niranjannt/Local-Music-Streaming-Pipeline/web_app/frontend/src/assets/need2.jpg

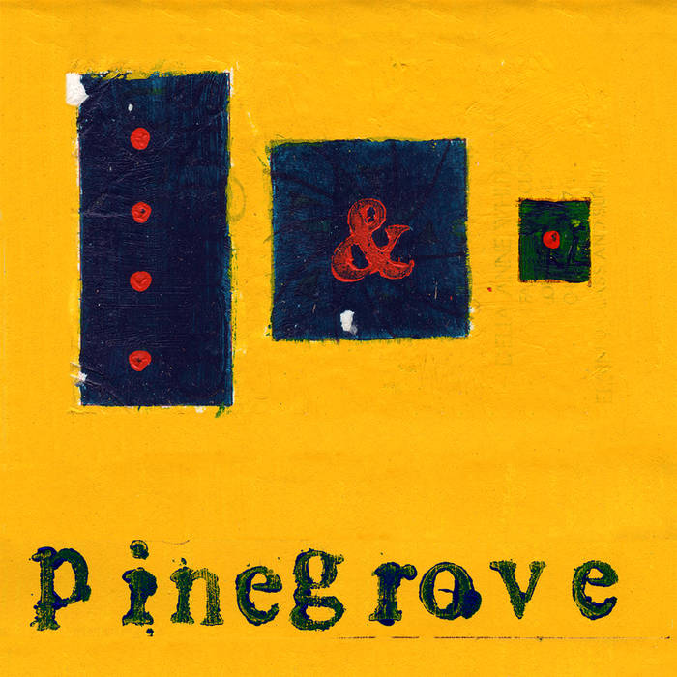
web_app/frontend/src/assets/need2.jpg
