niranjannt/Local-Music-Streaming-Pipeline/Resources/Lab 10/call_graph.png

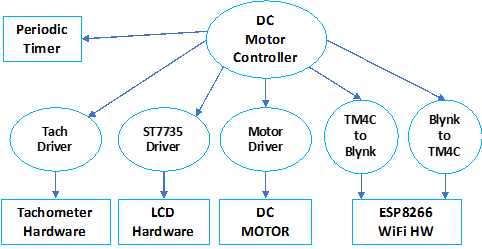
Resources/Lab 10/call_graph.png
