niranjannt/Local-Music-Streaming-Pipeline/Resources/Lab 10/figure_10.1.jpg

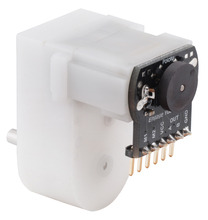
Resources/Lab 10/figure_10.1.jpg
