niranjannt/Local-Music-Streaming-Pipeline/Resources/Lab 10/figure_10.6.png

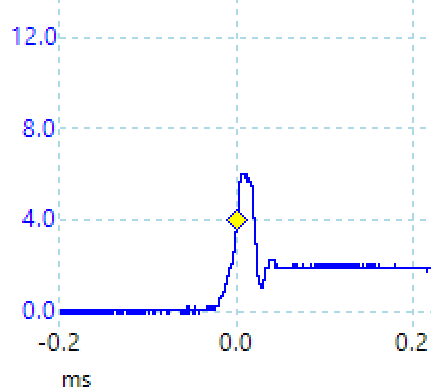
Resources/Lab 10/figure_10.6.png
