niranjannt/Local-Music-Streaming-Pipeline/Resources/Lab 10/figure_10.12.png

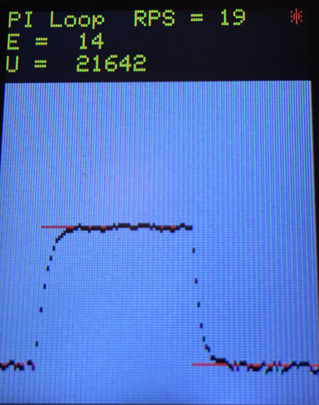
Resources/Lab 10/figure_10.12.png
