niranjannt/Local-Music-Streaming-Pipeline/web_app/frontend/src/assets/616inLA.jpg

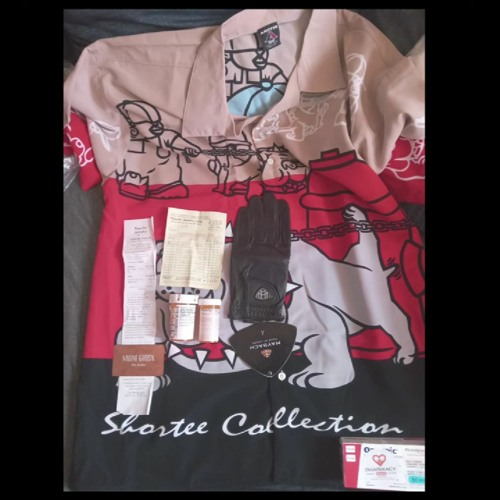
web_app/frontend/src/assets/616inLA.jpg
