niranjannt/Local-Music-Streaming-Pipeline/web_app/frontend/src/assets/undefined.jpg

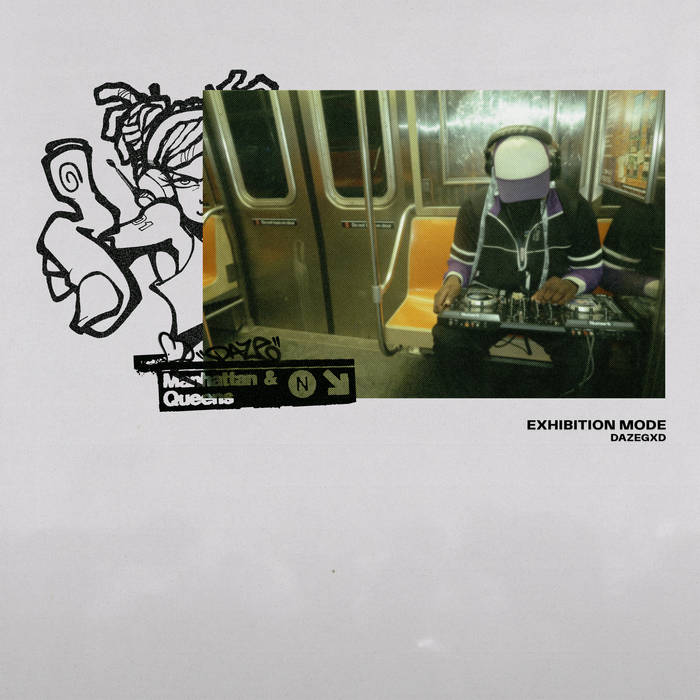
web_app/frontend/src/assets/undefined.jpg
