niranjannt/Local-Music-Streaming-Pipeline/hw/ECE445L_RSLK_V2/docs/BOMv2.xlsx

Sheet: ThroughHole
RSLK v2
Q | Manufacturer | Description | Mouser | Cost | Extension
1 | L293DNE | Darlington H-bridge | 595-L293DNE | $3.06 | $3.06
2 | CES-106-01-G-S | 6-pin female | 200-CES10601GS | $1.75 | $3.50
1 | SSQ-102-01-G-S | 2-pin female | 200-SSQ10201GS | $0.99 | $0.99
2 | 10129381-920003BLF | 2 by 10 male | 649-1012938192003BLF | $0.40 | $0.80
1 | 500SSP1S1M7QEA | power switch | 612-500-A171 | $3.29 | $3.29
1 | LM2937-5 | 5 V regulator | 926-LM2937ET-5.0NOPB | $2.06
1 | LM2937-3.3 | 3.3V regulator | 926-LM2937ET-3.3NOPB | $1.96
2 | JST-GH 6 Pin Male | 1.25 mm pitch connector | https://www.amazon.com/dp/B0B3N8MN3N |  |  | For TF Luna
2 | GP2Y0A21YK0F | Sensors | ebay or Pololu
3 | GP2Y0A41SK0F | Distance sensor | ebay or Pololu
5 | TAP106K020SCS | 10uF tantalum | 581-TAP106K020SCS | $0.70 | $3.50
1 | HLMP-4700 | 2mA Red LED | 638-HLMP4700 | $0.25 | $0.25
2 | CFR-12JB-4K7 | 4.7k resistor
1 |  | 700 ohm
1 |  | 10k
1 |  | 1.5k
Four choices for bump switch
6 | D2F-01L30-D3 | bump switch | 653-D2F01L30D3 | $1.75 | $10.50
6 | KW11-2 | bump switch | Pololu item #: 1404 | $1.65
 |  |  | 633-GW22LCV
1 | GW22LCP | DPDT power switch | 633-GW22LCP | $4.09
 | parts that could be soldered by JLC PCB |  |  |  | $7.61

Sheet: SurfaceMount
 | RSLK v2 |  |  |  | https://jlcpcb.com/parts/all-electronic-components |  |  | $279.37
 | Quan | Manufacturer | Description | Package | JCBPCB | Stock May24 | Cost | Extension | Comment
U1 | 1 | DRV8847PWPR | MOS H-bridge | HTSSOP-16-EP | C544361 | 677 | $1.10 | $1.10
J7,J8 | 0 | 87224-2 | 2-pin male | Plugin,P=2.54mm | C5172712 | 84 | $1.17 | $1.17 | For for launchPad power, one for MSPM0 | Mouser 571-872242
 | 0 | MTP125-1210M2 | 2 by 10 male | SMD,P=2.54mm | C5142437 | 1000 | $0.20 | $0.00
J1_J3,J4_J2 | 2 | DZ254S-22-20-75 | 2 by 10 male | SMD,P=2.54mm | C5160784 | 727 | $0.16 | $0.32
 | 0 | SM06B-GHS-TB(LF)(SN) | JST-GH 6 Pin Male | 1.25 mm pitch connector | C133065 | 9669 | $0.18 | $0.00 | For TF Luna | 538-502386-0670 | https://www.amazon.com/dp/B0B3N8MN3N
 | 0 | LM2937ES-5.0RG | 5 V regulator | TO-263-3 | C5145303 | 1090 | $0.31 | $0.00
U2 | 1 | LM2937IMP-5.0/NOPB | 5 V regulator | SOT-223-4 | C42249 | 1023 | $1.48 | $1.48
U3 | 1 | LM2937IMP-3.3/NOPB | 3.3V regulator | SOT-223 | C140265 | 941 | $1.43 | $1.43
J6 | 0 | 1MS1T3B1M1QES-5 | SPDT | 3-pin, 0.185in | C2913788 | 343 | $0.94 | $0.00 |  | 612-500SSP1S2M2QEA
R1-R4 | 4 | RMC1/16K103FTP | 10k resistors | 603 | C340542 | 1377 | $0.0041 | $0.02 | pullup for tachometer
C1-C8 | 8 | TAJB106K020RNJ | 10uF tantalum,20V | 1210 | C8017 | 9689 | $0.15 | $1.21 |  | 581-TAJB106K020R
LED1 | 1 | APTD1608LSECK/J3-PF | 2mA 1.8V red LED | SMD,1.6x0.8mm | C5879214 | 1896 | $0.33 | $0.33 |  | 604-APTD1608LSECKJ3F
R7 | 1 | HPCR0603F750RK9 | 750 ohm resistor | 603 | C365210 | 3820 | 0.0062 | $0.01
C9 | 1 | HHV0603R7104K101NTHJ | 0.1uF ceramic | 603 | C5186689 | 20000 | $0.01 | $0.01
R5,R6 | 2 | RLT06R10JTP | 0.100ohm resistor | 1206 | C2889036 | 599 | $0.0043 | $0.01
R8 | 1 | CR-03FL7---1K5 | 1.5k resistor | 603 | C216914 | 5000 | $0.0009 | $0.0009 | I2C pullup
 | Mouser
J5 | 1 | CES-106-01-G-S | 6-pin female | 6 pin 2.54mm | 200-CES10601GS | 289 | $2.06 | $2.06 | for motor/tach to Romi
 | 0 | TF Luna Uart | TOF distance | JST-GH 6 Pin | 234-TFLUNAUART | 278 | 24.99 | $0.00 | optional
 | 0 | GP2Y0A21YK0F | Long distance | 3 pin | 852-GP2Y0A21YK0F | 0 | $11.85 | $0.00 | ebay or Pololu
 | 0 | ESQT-103-02-F-S-309 | IR sensor to PCB | 3-pin 1.25mm female | 200-ESQT10302FS309 | 136 | $1.81 | $0.00
J11,J12,J13 | 3 | M22-7130342 | IR sensor to PCB | 3-pin 1.25mm female | 855-M22-7130342 | 2980 | $1.12 | $3.36
J11,J12,J13 | 3 | GP2Y0A41SK0F | short Distance sensor |  | 852-GP2Y0A41SK0F | 1927 | $10.10 | $30.30 | ebay or Pololu
 | 1 | 500SSP1S2M2QEA | SPDT | 3-pin, 0.185in | 612-500SSP1S2M2QEA | 740 | $3.13 | $3.13
 | 1 | SSQ-102-01-G-S | 2-pin female | on MSPM0 | 200-SSQ10201GS |  | $0.99 | $0.99
 | 1 | 500SSP1S1M7QEA | power switch |  | 612-500-A171 |  | $3.29 | $3.29
 | 5 | 382811-8 | 2-pin shunt | 2.54mm female | 571-3828118 | 39000 | $0.17 | $0.85
J7,J8 | 1 | TSW-104-07-L-S | 4-pin male | 2.54mm male | 200-TSW10407LS | 5000 | $0.26 | $0.26 | snap in two
 | 2 | 2112-440-AL-7 | 4-40 inch for breadboard |  | 761-2112-440-AL-7 | 1180 | $0.52 | $1.04
 | 4 | 9902 | 0.5in 4-40 screw |  | 534-9902 | 11000 | $0.12 | $0.48
 |  |  |  |  |  |  |  | $45.76
 | Pololu | Manufacturer | Description | Package | Pololu Part number | Stock May24 |  |  | https://www.pololu.com/
J5 | 1 | Romi Chassis Kits | Romi, motors, caster | kit | 3500 to 3509 (colors) | 500 | $39.95 | $39.95
J1-J4 | 4 | KW11-2 | bump switch |  | 1404 | 246 | $1.65 | $6.60
 | 2 | Romi motors | Gearmotor and Encoder | 6 pin male | 3675 | 49 | $15.49 | $30.98
 |  |  |  |  |  |  |  | $77.53
 | Texas Instruments |  |  |  | Mouser
 | 0 | LP-MSPM0G3507 | MSPM0 LaunchPad | Launchpad | 595-LP-MSPM0G3507 | 121 | $22.60 | $0.00
 | 1 | EK-TM4C123GXL | TM4C123 LaunchPad | Launchpad | 595-EK-TM4C123GXL | 1236 | $22.60 | $22.60 | Remove R9, R10, R25, R29
 | Amazon
J9 | 1 | JST-GH 6 Pin Male | TF Luna connector | 1.25 mm pitch connector |  |  | $0.10 | $0.10 | https://www.amazon.com/dp/B0B3N8MN3N
 | 1 | 0.96 Inch OLED I2C | SSD1306 | 4 pin 0.1in |  |  | $3.00 | $3.00 | https://www.amazon.com/Hosyond-Display-Self-Luminous-Compatible-Raspberry/dp/B09T6SJBV5
5 robots
 | JLCPCB |  |  |  |  |  |  | $136.10
 | Texas Instruments |  |  |  |  |  |  | $113.00
 | Mouser Parts |  |  |  |  |  | $44.24 | $221.21
 | Pololu |  |  |  |  |  | $77.53 | $387.65
 | Amazon |  |  |  |  |  | $3.00 | $15.00
 |  |  |  |  |  |  |  | $872.96

Sheet: cost
 | All solder | Part solder
driver | L293D | DRV8847
5 PCBs | $11.70 | $11.70
parts | $38.05
Manufac |  | $71.39
shippinh | $17.80 | $42.63
Mouser | $45.76 | $45.76
Polulo | $77.53 | $77.53
Amazon | $3.00 | $3.00
each | $139.80 | $151.44

Sheet: v2.0.2
 | RSLK v2.0.2 |  |  |  | https://jlcpcb.com/parts/all-electronic-components |  |  | $309.54
 | Quan | Manufacturer | Description | Package | JCBPCB | Stock May24 | Cost | Extension | Comment | Mouser
U1 | 1 | DRV8847PWPR | MOS H-bridge | HTSSOP-16-EP | C544361 | 374 | $1.10 | $1.10 |  | 595-DRV8847PWPR
J10 J14 | 2 |  | 3-pin male | Plugin,P=2.54mm |  |  |  |  |  | 571-2-826629-0
J7,J8,J16,J15 | 4 | 87224-2 | 2-pin male | Plugin,P=2.54mm | C5172712 | 84 | $1.17 | $1.17 | One for battery current, Two for launchPad power, one for MSPM0 | 571-872242
 | 0 | MTP125-1210M2 | 2 by 10 male | SMD,P=2.54mm | C5142437 | 1000 | $0.20 | $0.00
J3_J1,J2_J4 | 2 | DZ254S-22-20-75 | 2 by 10 male | SMD,P=2.54mm | C5160784 | 161 | $0.16 | $0.32 |  | 855-M20-8761042P
 | 0 | SM06B-GHS-TB(LF)(SN) | JST-GH 6 Pin Male | 1.25 mm pitch connector | C133065 | 9669 | $0.18 | $0.00 | For TF Luna | 538-502386-0670 | https://www.amazon.com/dp/B0B3N8MN3N
 | 0 | LM2937ES-5.0RG | 5 V regulator | TO-263-3 | C5145303 | 1090 | $0.31 | $0.00
U2 | 1 | LM2937IMP-5.0/NOPB | 5 V regulator | SOT-223-4 | C42249 | 618 | $1.48 | $1.48 |  | 926-LM2937IMP5.0NOPB
U3 | 1 | LM2937IMP-3.3/NOPB | 3.3V regulator | SOT-223 | C140265 | 720 | $1.43 | $1.43 |  | 926-LM2937IMP3.3NOPB
J6 | 0 | 1MS1T3B1M1QES-5 | SPDT | 3-pin, 0.185in | C2913788 | 343 | $0.94 | $0.00 |  | 612-500SSP1S2M2QEA
R1,R2 | 2 | AC0603FR-074K7L | 4.7k resistors | 603 | C441894 | 30000 | $0.0041 | $0.01 | pullup for tachometer | 603-RC0603FR-07470RL
R4 | 1 | 0603WAF1002T5E | 10k resistors | 603 | C25804 | millions | $0.0041 | $0.0041 | pullup for tachometer | 603-RC0603FR-0710KL
C1-C8 | 8 | TAJB106K020RNJ | 10uF tantalum,20V | 1210 | C8017 | 100000 | $0.15 | $1.21 |  | 581-TAJB106K020R
LED1 | 1 | APTD1608LSECK/J3-PF | 2mA 1.8V red LED | SMD,1.6x0.8mm | C5879214 | 900 | $0.33 | $0.33 |  | 604-APTD1608LSECKJ3F
R7 | 1 | HPCR0603F750RK9 | 750 ohm resistor | 603 | C365210 | 2000 | 0.0062 | $0.01 |  | 603-RC0603JR-07750RL
C9 | 1 | HHV0603R7104K101NTHJ | 0.1uF ceramic | 603 | C5186689 | 11000 | $0.01 | $0.01 |  | 80-C0603C104K3R
R5,R6 | 2 | RLT06R10JTP | 0.100ohm resistor | 1206 | C2889036 | 2000 | $0.0043 | $0.01 |  | 71-RCWL1206R100JMEA
R3 | 1 | CR-03FL7---1K5 | 1.5k resistor | 603 | C216914 | 5000 | $0.0009 | $0.0009 | I2C pullup | 603-RC0603FR-071K5L
 | Mouser
J5 | 2 | CES-106-01-G-S | 6-pin female | 6 pin 2.54mm | 200-CES10601GS | 289 | $2.06 | $4.12 | for motor/tach to Romi
 | 0 | TF Luna Uart | TOF distance | JST-GH 6 Pin | 234-TFLUNAUART | 278 | 24.99 | $0.00 | optional
 | 0 | GP2Y0A21YK0F | Long distance | 3 pin | 852-GP2Y0A21YK0F | 0 | $11.85 | $0.00 | ebay or Pololu
 | 0 | ESQT-103-02-F-S-309 | IR sensor to PCB | 3-pin 1.25mm female | 200-ESQT10302FS309 | 136 | $1.81 | $0.00
J11,J12,J13 | 3 | M22-7130342 | IR sensor to PCB | 3-pin 1.25mm female | 855-M22-7130342 | 2980 | $1.12 | $3.36
J11,J12,J13 | 3 | GP2Y0A41SK0F | short Distance sensor |  | 852-GP2Y0A41SK0F | 1927 | $10.10 | $30.30 | ebay or Pololu
J6 | 1 | 500SSP1S2M2QEA | SPDT | 3-pin, 0.185in | 612-500SSP1S2M2QE | 740 | $3.13 | $3.13 |  | right angle 612-500-A171
from J7 | 1 | SSQ-102-01-G-S | 2-pin female | on MSPM0 | 200-SSQ10201GS |  | $0.99 | $0.99
 | 5 | 382811-8 | 2-pin shunt | 2.54mm female | 571-3828118 | 39000 | $0.17 | $0.85
J7,J8 | 1 | TSW-104-07-L-S | 4-pin male | 2.54mm male | 200-TSW10407LS | 5000 | $0.26 | $0.26 | snap in two
 | 1 | SSW-104-01-F-D | 2 by 4 socket | 2.54mm female | 200-SSW10401FD | 1233 | $1.32 | $1.32 | ESP8288
 | 2 | 2112-440-AL-7 | 4-40 inch for breadboard |  | 761-2112-440-AL-7 | 1180 | $0.52 | $1.04
 | 2 | 9900 | 0.25in 4-40 screw |  | 534-9900 | 50000 | $0.12 | $0.24
 | 2 | 9902 | 0.5in 4-40 screw |  | 534-9902 | 11000 | $0.12 | $0.24
 | 4 | 9355 | 0.25in 2-56 screw |  | 534-9355 |  |  |  | https://www.amazon.com/binifiMux-100pcs-2-56-Stainless-Steel/dp/B08NTZDR3H/
 | 4 |  | 2-56 hex nuts |  |  |  |  |  | https://www.amazon.com/binifiMux-100pcs-2-56-Stainless-Steel/dp/B08NTZDR3H/
 |  |  |  |  |  |  |  | $45.85
 | Pololu | Manufacturer | Description | Package | Pololu Part number | Stock May24 |  |  | https://www.pololu.com/
J5 | 1 | Romi Chassis Kits | Romi, motors, caster | kit | 3500 to 3509 (colors) | 500 | $39.95 | $39.95
J1-J4 | 4 | KW11-2 | bump switch |  | 1404 | 246 | $1.65 | $6.60
 | 2 | Romi motors | Gearmotor and Encoder | 6 pin male | 3675 | 49 | $15.49 | $30.98
 |  |  |  |  |  |  |  | $77.53
 | Texas Instruments |  |  |  | Mouser
 | 0 | LP-MSPM0G3507 | MSPM0 LaunchPad | Launchpad | 595-LP-MSPM0G3507 | 121 | $22.60 | $0.00
 | 1 | EK-TM4C123GXL | TM4C123 LaunchPad | Launchpad | 595-EK-TM4C123GXL | 1236 | $22.60 | $22.60 | Remove R9, R10, R25, R29
 | Amazon
J9 | 1 | JST-GH 6 Pin Male | TF Luna connector | 1.25 mm pitch connector |  |  | $0.10 | $0.10 | https://www.amazon.com/dp/B0B3N8MN3N
 | 1 | 0.96 Inch OLED I2C | SSD1306 | 4 pin 0.1in |  |  | $3.00 | $3.00 | https://www.amazon.com/Hosyond-Display-Self-Luminous-Compatible-Raspberry/dp/B09T6SJBV5
 | 1 | charger and 8 AA batteries |  |  |  |  | $27.99 | $27.99 | https://www.amazon.com/dp/B00M2RA8XS
 | 0 | ESP8266 |  |  |  |  | $3.00 | $0.00 | https://www.amazon.com/HiLetgo-Wireless-Transceiver-Development-Compatible/dp/B010N1ROQS
 | 1 | ESP8266 |  |  |  |  | $2.00 | $2.00 | https://www.amazon.com/dp/B0872XG31W
 | 0 | charger |  |  |  |  |  |  | https://www.amazon.com/dp/B00EB7812C
5 robots
 | JLCPCB |  |  |  |  |  |  | $136.10
 | Texas Instruments |  |  |  |  |  |  | $113.00
 | Mouser Parts |  |  |  |  |  | $43.01 | $215.06
 | Pololu |  |  |  |  |  | $77.53 | $387.65
 | Amazon |  |  |  |  |  | $31.09 | $155.45
 |  |  |  |  |  |  |  | $1007.26

Sheet: JulyOrder2024
$946.94
