niranjannt/Local-Music-Streaming-Pipeline/sw/src/Timers.c

/*
 * Timers.c
 *
 *  Created on: Oct 5, 2025
 *      Author: nathan
 */

#include <stdint.h>
#include "../inc/tm4c123gh6pm.h"
#include "../inc/CortexM.h"
#include "Timers.h"

#define NVIC_EN0_INT19          0x00080000  // Interrupt 19 enable
#define TIMER_CFG_16_BIT        0x00000004  // 16-bit timer configuration,
                                            // function is controlled by bits
                                            // 1:0 of GPTMTAMR and GPTMTBMR
#define TIMER_TAMR_TACDIR       0x00000010  // GPTM Timer A Count Direction
#define TIMER_TAMR_TAMR_PERIOD  0x00000002  // Periodic Timer mode
#define TIMER_CTL_TAEN          0x00000001  // GPTM TimerA Enable
#define TIMER_IMR_TATOIM        0x00000001  // GPTM TimerA Time-Out Interrupt
                                            // Mask
#define TIMER_ICR_TATOCINT      0x00000001  // GPTM TimerA Time-Out Raw
                                            // Interrupt
#define TIMER_TAILR_TAILRL_M    0x0000FFFF  // GPTM TimerA Interval Load
                                            // Register Low


void (*PeriodicTask0)(void);   // user function



void Timer0A_Init(void(*task)(void), uint32_t period, uint32_t priority){
  SYSCTL_RCGCTIMER_R |= 0x01;      // 0) activate timer0
  PeriodicTask0 = task;            // user function (this line also allows time to finish activating)
  TIMER0_CTL_R &= ~0x00000001;     // 1) disable timer0A during setup
  TIMER0_CFG_R = 0x00000000;       // 2) configure for 32-bit timer mode
  TIMER0_TAMR_R = 0x00000002;      // 3) configure for periodic mode, default down-count settings
  TIMER0_TAILR_R = period-1;       // 4) reload value
  TIMER0_TAPR_R = 0;               // 5) 12.5ns timer0A
  TIMER0_ICR_R = 0x00000001;       // 6) clear timer0A timeout flag
  TIMER0_IMR_R |= 0x00000001;      // 7) arm timeout interrupt
  NVIC_PRI4_R = (NVIC_PRI4_R&0x00FFFFFF)|(priority<<29);
  NVIC_EN0_R = NVIC_EN0_INT19;     // 9) enable interrupt 19 in NVIC
  TIMER0_CTL_R |= 0x00000001;      // 10) enable timer0A
}

void Timer0A_Handler(void){
  TIMER0_ICR_R = TIMER_ICR_TATOCINT;// acknowledge timer0A timeout
  (*PeriodicTask0)();                // execute user task
}
void Timer0A_Stop(void){
  NVIC_EN0_R = 1<<19;            // 9) disable interrupt 19 in NVIC
  TIMER0_CTL_R = 0x00000000;     // 10) disable timer0A
}

void Timer0A_Start() {
    TIMER0_CTL_R = 0x00000001;
}


void (*PeriodicTask1)(void);   // user function

void Timer1A_Init(void(*task)(void), uint32_t period, uint32_t priority){
  SYSCTL_RCGCTIMER_R |= 0x02;   // 0) activate TIMER1
  PeriodicTask1 = task;         // user function
  TIMER1_CTL_R = 0x00000000;    // 1) disable TIMER1A during setup
  TIMER1_CFG_R = 0x00000000;    // 2) configure for 32-bit mode
  TIMER1_TAMR_R = 0x00000002;   // 3) configure for periodic mode, default down-count settings
  TIMER1_TAILR_R = period-1;    // 4) reload value
  TIMER1_TAPR_R = 0;            // 5) bus clock resolution
  TIMER1_ICR_R = 0x00000001;    // 6) clear TIMER1A timeout flag
  TIMER1_IMR_R = 0x00000001;    // 7) arm timeout interrupt
  NVIC_PRI5_R = (NVIC_PRI5_R&0xFFFF00FF)|(priority<<13); // priority
// interrupts enabled in the main program after all devices initialized
// vector number 37, interrupt number 21
  NVIC_EN0_R = 1<<21;           // 9) enable IRQ 21 in NVIC
  TIMER1_CTL_R = 0x00000001;    // 10) enable TIMER1A
}
// write 1 to TIMER1_ICR_R
// will clear bit 0 TIMER1_RIS_R
void Timer1A_Handler(void){
    // acknowledging
  TIMER1_ICR_R = TIMER_ICR_TATOCINT;// acknowledge TIMER1A timeout
  (*PeriodicTask1)();               // execute user task
}
void Timer1A_Stop(void){
  NVIC_DIS0_R = 1<<21;        // 9) disable IRQ 21 in NVIC
  TIMER1_CTL_R = 0x00000000;  // 10) disable timer1A

}

void Timer1A_Start() {
    TIMER1_CTL_R = 0x00000001;
}


void (*PeriodicTask2)(void);   // user function


void Timer2A_Init(void(*task)(void), uint32_t period, uint32_t priority){
  SYSCTL_RCGCTIMER_R |= 0x04;   // 0) activate timer2
  PeriodicTask2 = task;         // user function
  TIMER2_CTL_R = 0x00000000;    // 1) disable timer2A during setup
  TIMER2_CFG_R = 0x00000000;    // 2) configure for 32-bit mode
  TIMER2_TAMR_R = 0x00000002;   // 3) configure for periodic mode, default down-count settings
  TIMER2_TAILR_R = period-1;    // 4) reload value
  TIMER2_TAPR_R = 0;            // 5) bus clock resolution
  TIMER2_ICR_R = 0x00000001;    // 6) clear timer2A timeout flag
  TIMER2_IMR_R = 0x00000001;    // 7) arm timeout interrupt
  NVIC_PRI5_R = (NVIC_PRI5_R&0x00FFFFFF)|(priority<<29); // priority
// interrupts enabled in the main program after all devices initialized
// vector number 39, interrupt number 23
  NVIC_EN0_R = 1<<23;           // 9) enable IRQ 23 in NVIC
  TIMER2_CTL_R = 0x00000001;    // 10) enable timer2A
}

void Timer2A_Handler(void){
  TIMER2_ICR_R = TIMER_ICR_TATOCINT;// acknowledge TIMER2A timeout
  (*PeriodicTask2)();               // execute user task
}

void Timer2A_Stop(void){
  NVIC_DIS0_R = 1<<23;        // 9) disable interrupt 23 in NVIC
  TIMER2_CTL_R = 0x00000000;  // 10) disable timer2A
}

void Timer2A_Start() {
    TIMER2_CTL_R = 0x00000001;
}


void (*PeriodicTask3)(void);   // user function


void Timer3A_Init(void(*task)(void), uint32_t period, uint32_t priority){
  SYSCTL_RCGCTIMER_R |= 0x08;   // 0) activate TIMER3
  PeriodicTask3 = task;         // user function
  TIMER3_CTL_R = 0x00000000;    // 1) disable TIMER3A during setup
  TIMER3_CFG_R = 0x00000000;    // 2) configure for 32-bit mode
  TIMER3_TAMR_R = 0x00000002;   // 3) configure for periodic mode, default down-count settings
  TIMER3_TAILR_R = period-1;    // 4) reload value
  TIMER3_TAPR_R = 0;            // 5) bus clock resolution
  TIMER3_ICR_R = 0x00000001;    // 6) clear TIMER3A timeout flag
  TIMER3_IMR_R = 0x00000001;    // 7) arm timeout interrupt
  NVIC_PRI8_R = (NVIC_PRI8_R&0x00FFFFFF)|(priority<<29); // priority
// interrupts enabled in the main program after all devices initialized
// vector number 51, interrupt number 35
  NVIC_EN1_R = 1<<(35-32);      // 9) enable IRQ 35 in NVIC
  TIMER3_CTL_R = 0x00000001;    // 10) enable TIMER3A
}

void Timer3A_Handler(void){
  TIMER3_ICR_R = TIMER_ICR_TATOCINT;// acknowledge TIMER3A timeout
  (*PeriodicTask3)();                // execute user task
}

void Timer3A_Stop(void){
  NVIC_DIS1_R = 1<<(35-32);        // 9) disable interrupt 35in NVIC
  TIMER3_CTL_R = 0x00000000;       // 10) disable timer4A
}

void Timer3A_Start() {
    TIMER3_CTL_R = 0x00000001;
}
