niranjannt/Local-Music-Streaming-Pipeline/sw/src/Volume.h

/*
 * Volume.h
 *
 *  Created on: Dec 2, 2025
 *      Author: Ashton
 */

#ifndef VOLUME_H_
#define VOLUME_H_


void initVolume();
void setBass(unsigned input);
void setMid(unsigned input);
void setTreb(unsigned input);

void setVolume(unsigned input);


#endif /* VOLUME_H_ */
