niranjannt/Local-Music-Streaming-Pipeline/sw/src/AudioCommands.h

/*
 * AudioCommands.h
 *
 *  Created on: Oct 26, 2025
 *      Author: Thompson
 */

#ifndef AUDIOCOMMANDS_H_
#define AUDIOCOMMANDS_H_


void AudioCommandInit();
void AudioCommandsHandler();
void AudioCommandOut();



#endif /* AUDIOCOMMANDS_H_ */
