niranjannt/Local-Music-Streaming-Pipeline/sw/src/LCD.c

#include <stdint.h>
#include "../inc/tm4c123gh6pm.h"
#include "Timers.h"
#include "LCD.h"
#include "../inc/SysTickInts.h"
#include "../inc/TLV5616.h"

/*
 * Signals to use:
 * PB2 - Bass GPIO0
 * PB3 - Bass GPIO1
 * PB4 - Mid GPIO0
 * PB5 - Mid GPIO1
 * PB6 - Treble GPIO0
 * PB7 - Treble GPIO1
 * PC4 - Volume GPIO0
 * PC5 - Volume GPIO1
 * PC6 - Volume GPIO2
 */



void InitLCD() {

}

void UpdateLCD() {

}
